hmd83/tanen/docs/TRD-001.md

  
**TanenBase Project**

Smart Hive Monitoring System

**Technical Requirements Document**

TRD-001

| Document Version | 1.0 |
| :---- | :---- |
| **Status** | DRAFT |
| **Date** | March 2026 |
| **Project** | TanenBase \- Smart Hive System |

> **Note for readers of the open-source release.** This TRD is a **DRAFT** written before implementation, kept in the repo as design intent and traceability for the acceptance criteria (AC-01 … AC-10). Where the shipped firmware deliberately differs from it \- payload width, timer implementation, join/DevNonce handling, GATT write permissions \- `ARCHITECTURE.md` and `PLAN.md` are authoritative, not this document. See "Deviations from this TRD" below.

# **1\. Document Control**

| Field | Details |
| :---- | :---- |
| **Project Name** | TanenBase — Smart Hive Monitoring System |
| **Document Type** | Technical Requirements Document (TRD) |
| **Document ID** | TRD-001 |
| **Version** | 1.0 — Initial Release |
| **Status** | DRAFT |
| **Date** | March 2026 |
| **Classification** | Confidential |

## **1.1 Revision History**

| Version | Description |
| :---- | :---- |
| **1.0** | Initial TRD drafted — all hardware, firmware, LoRa, FSM, and payload requirements defined. |

## **1.2 Definitions & Abbreviations**

| Term | Definition |
| :---- | :---- |
| **ADC** | Analog-to-Digital Converter |
| **ADR** | Adaptive Data Rate (LoRaWAN feature) |
| **BLE** | Bluetooth Low Energy |
| **FSM** | Finite State Machine |
| **LNS** | LoRa Network Server (e.g., TTN) |
| **LoRa** | Long Range radio modulation technology (Semtech SX1262) |
| **LoRaWAN** | LoRa Wide Area Network — open MAC layer protocol |
| **OTAA** | Over-the-Air Activation — LoRaWAN join procedure |
| **T\_MEAS** | Measurement Timer — interval between sensor readings |
| **T\_TX** | Transmission Timer — interval between LoRa uplinks |
| **TTN** | The Things Network — public LoRaWAN network server |
| **TRD** | Technical Requirements Document |

# **2\. Project Overview**

TanenBase is an ultra-low-power IoT end-node designed for remote, unattended beehive monitoring. Each node is deployed inside or beneath a beehive and continuously measures hive weight, internal temperature, and battery voltage. Collected data is transmitted over the LoRaWAN network to a cloud server for remote analysis and alerting.

The system is engineered for extreme power efficiency, enabling multi-year operation on a single battery charge. A Finite State Machine (FSM) governs all operational modes, ensuring that the sensor sampling schedule is fully decoupled from the radio transmission schedule. Both timers are remotely configurable via LoRaWAN downlink or locally via Bluetooth (BLE).

## **2.1 System Goals**

* Continuous, unattended monitoring of hive weight, temperature, and battery voltage.

* Ultra-low-power operation — less than 20 µA in sleep state.

* Immediate anomaly alerting for sudden weight loss (swarm detection or theft).

* Remote parameter configuration via LoRaWAN downlink and local BLE.

* Robust, binary-encoded LoRaWAN uplinks with 4-byte payload.

* Reliable OTAA network joins on the EU868 frequency plan.

# **3\. Hardware Platform**

## **3.1 Processing & Radio Module**

| Parameter | Specification |
| :---- | :---- |
| **Module** | Seeed Studio XIAO nRF54LM20A (Standard, non-Sense variant) \+ Wio-SX1262 LoRa Kit |
| **MCU** | Arm Cortex-M33 128 MHz RISC-V coprocessor 128 MHz FLPR  |
| **Flash Memory** | NVM 1.5 MB |
| **RAM** | 256 KB  RAM |
| **BLE Radio** | Integrated Bluetooth 6.0 LE (2.4 GHz) |
| **LoRa Modem** | Semtech SX1262 (mounted on Wio-SX1262 kit) |
| **Operating Voltage** | 3.3 V |

## **3.2 Sensors**

| Component | Specification & Purpose |
| :---- | :---- |
| **Load Cell ADC** | Adafruit NAU7802 24-Bit ADC — high-resolution weight measurement via I2C |
| **Temperature Sensor** | DS18B20 1-Wire digital temperature sensor — hive internal temperature |
| **Battery Monitor** | On-board Nordic nPM1300 PMIC, factory-trimmed VBAT ADC (no divider) |

## **3.3 User Interface**

| Interface Element | Hardware & Function |
| :---- | :---- |
| **LED** | System status indicator — BLE/Setup mode active \-successful LoRa transmission- LoRa join failure |
| **TanenButton** | Physical push button — triggers Setup Mode (hold 3 s) or wakes from sleep |

# **4\. Software & Operating System**

| Parameter | Specification |
| :---- | :---- |
| **Operating System** | nRF Connect SDK v3.2.4 |
| **Build System** | West (Zephyr meta-tool) |
| **LoRaWAN Stack** | Zephyr LoRaWAN subsystem (LRWAN) |
| **BLE Stack** | Zephyr Bluetooth subsystem (Nordic SoftDevice-compatible) |
| **Storage** | Zephyr Settings subsystem (NVS backend) for persistent config |
| **Power Management** | Zephyr Power Management API — lowest supported sleep state |

# **5\. LoRaWAN Requirements**

## **5.1 Network Parameters**

| Parameter | Requirement |
| :---- | :---- |
| **Radio Modem** | Semtech SX1262 — LoRa-only modem |
| **Frequency Plan** | EU868 — European 868 MHz ISM band (8 channels) |
| **Join Procedure** | OTAA (Over-the-Air Activation) — mandatory. ABP is prohibited. |
| **Device Class** | Class A — lowest power; uplink-initiated receive windows only |
| **Payload Encoding** | Binary — raw bytes only. JSON and text strings are strictly forbidden. |
| **Adaptive Data Rate** | ADR enabled — network server controls spreading factor and transmit power |
| **Confirmed Uplinks** | Unconfirmed uplinks preferred to minimize airtime; confirmed only for anomaly alerts |
| **Downlink Usage** | Used for remote configuration of T\_MEAS, T\_TX, and anomaly threshold |

## **5.2 EU868 Channel Plan**

| Channel | Frequency & Settings |
| :---- | :---- |
| **CH0** | 868.100 MHz — Spreading Factor SF7-SF12, BW 125 kHz |
| **CH1** | 868.300 MHz — Spreading Factor SF7-SF12, BW 125 kHz |
| **CH2** | 868.500 MHz — Spreading Factor SF7-SF12, BW 125 kHz |
| **CH3–CH7** | Additional channels per TTN EU868 plan (joined after OTAA) |
| **Join Channels** | CH0, CH1, CH2 used for OTAA join requests |
| **Duty Cycle** | 1% per sub-band — strictly enforced to comply with EU ETSI regulations |
| **Max EIRP** | 16 dBm (per EU868 specification) |

## **5.3 OTAA Credentials**

| Credential | Requirement |
| :---- | :---- |
| **JoinEUI (AppEUI)** | 64-bit identifier — provisioned during Setup Mode via BLE web app |
| **DevEUI** | 64-bit unique device identifier — factory-programmed or BLE-provisioned |
| **AppKey** | 128-bit AES root key — provisioned during Setup Mode via BLE web app |
| **Storage** | All credentials stored in non-volatile flash via Zephyr Settings (NVS) |

## **5.4 Downlink Command Format**

Class A RX1/RX2 after every uplink. One field per downlink (FPort selects field). User may send any subset.

| FPort | Field | Bytes | Encoding |
| :---- | :---- | :---- | :---- |
| **10** | T\_TX (`tx_interval`) | 4 | uint32 BE, seconds |
| **11** | T\_MEAS (`ms_interval`) | 4 | uint32 BE, seconds (clamped ≥ 60) |
| **12** | anomaly weight threshold | 2 | uint16 BE, grams |
| **13** | anomaly temp threshold | 2 | uint16 BE, °C × 100 |

Wrong length → ignored (warning logged). Values persisted to ZMS on receipt.

# **6\. Payload Specification**

The uplink payload is exactly 4 bytes. No padding, headers, version bytes, or metadata are permitted. The server (TTN Payload Formatter) is solely responsible for decoding raw values back to human-readable units.

## **6.1 Payload Map**

| Byte(s) | Field |
| :---- | :---- |
| **Byte 0–1 (uint16, big-endian)** | Weight — raw value \= kg × 100\. Range: 0–65535 (max 655.35 kg). Example: 45.23 kg → 4523 |
| **Byte 2 (uint8)** | Temperature — raw value \= °C rounded to nearest integer. Range: 0–255. Example: 36°C → 36 |
| **Byte 3 (uint8)** | Battery Voltage — raw value \= V × 10\. Range: 0–255 (max 25.5 V). Example: 12.4 V → 124 |

## **6.2 Payload Encoding Rules**

* Total payload length: exactly 4 bytes. Never more, never less.

* Weight field: multiply float kg value by 100, cast to uint16, pack as big-endian.

* Temperature field: round float °C value to nearest integer, cast to uint8.

* Voltage field: multiply float V value by 10, cast to uint8.

* Fields must be packed in the order: Weight (2B), Temperature (1B), Voltage (1B).

* No null bytes, no struct padding, no alignment bytes between fields.

* JSON, CSV, or ASCII text payloads are prohibited and constitute a firmware defect.

## **6.3 TTN Payload Decoder (Reference JavaScript)**

function decodeUplink(input) {

  var b \= input.bytes;  
  return { decoded\_payload: {  
    weight\_kg:  ((b\[0\] \<\< 8\) | b\[1\]) / 100.0,  
    temperature\_c: b\[2\],  
    voltage\_v:   b\[3\] / 10.0  
  }};

}

# **7\. Cycle Control & Power Management**

The sensor measurement schedule and the LoRaWAN transmission schedule are fully independent. Two configurable timers govern system wake cycles.

## **7.1 Timer Parameters**

| Parameter | Specification |
| :---- | :---- |
| **T\_MEAS** | Measurement Timer — minimum 1 minute. Configurable remotely via LoRaWAN downlink or BLE. |
| **T\_TX** | Transmission Timer — must satisfy: T\_TX ≥ T\_MEAS at all times. |
| **Remote Config** | Both timers are remotely adjustable via LoRaWAN downlink command or BLE Setup Mode. |
| **Constraint Enforcement** | Firmware must reject any downlink that sets T\_TX \< T\_MEAS and respond with a NACK. |
| **Default T\_MEAS** | 15 minutes (900 seconds) |
| **Default T\_TX** | 60 minutes (3600 seconds) |

## **7.2 Measurement Routine**

* Wake processor from deep sleep.

* Power up load cell (NAU7802) and DS18B20 .

* Acquire N consecutive weight samples (default N \= 10\) at regular intervals.

* Compute arithmetic mean weight; discard outliers exceeding ±2σ to suppress wind noise.

* Acquire single temperature reading from DS18B20.

* Acquire single battery voltage reading via internal ADC.

* Compare new mean weight to last stored weight; check for anomaly threshold breach.

* Store all readings in SRAM (latest snapshot only — no historical buffer required).

* Power down all sensors immediately after data acquisition.

* Transition to FSM State 4 (Active Sleep) or State 3 (Transmission) based on anomaly flag.

## **7.3 Transmission Routine**

* Wake processor from deep sleep.

* Load latest sensor snapshot from SRAM.

* Encode 4-byte binary payload per Section 6 specification.

* Power up SX1262 LoRa radio via SPI.

* Transmit uplink on next available channel (duty cycle compliant).

* Hold radio active for RX1 window (1 second delay) and RX2 window (2 seconds delay) to receive downlink.

* Process any received downlink configuration commands.

* Power down SX1262 radio (all GPIO lines low, SPI bus released).

* Return to FSM State 4 (Active Sleep).

## **7.4 Emergency Anomaly Override**

| Parameter | Specification |
| :---- | :---- |
| **Trigger Condition** | New mean weight \< (last stored weight − anomaly threshold) |
| **Default Threshold** | 2.0 kg (200 raw units). Configurable via downlink or BLE. |
| **Action** | Abort T\_TX wait. Immediately enter State 3 (Transmission).  LED blink |
| **Uplink Type** | Confirmed uplink used for anomaly alerts to guarantee delivery. |
| **Alert Payload** | Standard 4-byte payload — server infers anomaly from weight delta via TTN decoder. |

# **8\. Finite State Machine (FSM)**

The firmware implements a strict four-state FSM. No state may be entered except through its defined entry conditions. All transitions are deterministic.

| State 1: Setup Mode (BLE) |  |
| :---- | :---- |
| **Entry** | Initial device boot OR TanenButton held for ≥3 seconds. |
| **LED State** | solid ON throughout Setup Mode. |
| **BLE** | Activate Bluetooth LE. Advertise as 'TanenBase-XXXX' (last 4 hex of DevEUI). |
| **Web App** | Serve configuration interface via connected BLE client (HTML \+ JS web app one file index.html). |
| **Config Items** | LoRaWAN credentials (JoinEUI, DevEUI, AppKey), T\_MEAS, T\_TX, anomaly threshold, scale calibration (zero offset, scale factor) \-read(expt AppKey  )-write(save). |
| **Live Feed** | Broadcast real-time sensor data over BLE NOTIFY characteristic for scale tare/calibration. |
| **Test Join** | Execute LoRaWAN OTAA test join on user request from web app. Report result (Blink 1Hz \= OK, fast= fail). |
| **Exit — Normal** | Exit button in web app . BLE advertisement stopped. Transition to State 4\. |
| **Exit — Timeout** | 5-minute inactivity timeout reached without user interaction. BLE stopped. Transition to State 4\. |

| State 2: Measurement State |  |
| :---- | :---- |
| **Entry** | T\_MEAS timer expiration in State 4\. |
| **LED State** | No LED activity during measurement (power conservation). |
| **Sensor Power** | Wake up NAU7802 and DS18B20 .NAU7802 requires time 600ms  to stabilize |
| **Weight Acquisition** | Capture N \= 10 samples from NAU7802 ADC. Compute filtered mean weight (kg). |
| **Temp Acquisition** | Issue single read command to DS18B20. Store integer °C value. |
| **Voltage Acquisition** | VBAT Enable pin then Sample internal ADC on voltage-divider channe(P1.13 AIN6\_VBAT)l. Store (V × 10\) uint8 value. |
| **Anomaly Check** | If (new weight) \< (last weight − threshold): set ANOMALY flag. |
| **Data Save** | Update SRAM sensor snapshot with new values. |
| **Exit — Anomaly** | ANOMALY flag set → transition immediately to State 3 (Transmission). |
| **Exit — Normal** | No anomaly → transition to State 4 (Active Sleep). |

| State 3: Transmission State |  |
| :---- | :---- |
| **Entry** | T\_TX timer expiration in State 4 OR ANOMALY flag set in State 2\. |
| **LED State** | LED — blinks once per transmit attempt. blinks fat — lit on join failure or anomaly uplink. |
| **Payload Build** | Encode 4-byte binary payload: bytes \[0:1\] \= weight × 100 (uint16 BE), byte \[2\] \= temp (uint8), byte \[3\] \= voltage × 10 (uint8). |
| **Radio Power** | Assert SPI CS and power enable for SX1262. |
| **Transmit** | Send uplink frame (unconfirmed normally; confirmed if ANOMALY flag set). |
| **RX Windows** | Wait for RX1 ( 5 s window) and RX2 (6 s window). Process any downlink. |
| **Downlink Handling** | Apply new T\_MEAS, T\_TX, or anomaly threshold from downlink. Validate T\_TX ≥ T\_MEAS. |
| **Radio Power Down** | De-assert all SX1262 control lines. Release SPI bus. |
| **Clear Flag** | Clear ANOMALY flag. |
| **Exit** | Always transition to State 4 (Active Sleep). |

| State 4: Active Sleep State |  |
| :---- | :---- |
| **Entry** | Completion of State 1, State 2, or State 3\. |
| **LED State** | All LEDs OFF. |
| **Sensor Power** | NAU7802 powered down (AVDDS=1, PUA=0 \-\> \~0.1 uA)-powered down DS18B20 I2C pins during low-power modes, they should generally be configured as inputs (high-impedance) or as outputs driven high to avoid leaking current through external pull-up resistors |
| **Radio Power** | SX1262 in SLEEP mode. SPI bus idle. BLE radio disabled. |
| **MCU Sleep** | nRF54LM20A enters System OFF \+ GRTC \+ RAM retention (stack \+ essentials) |
| **Power Budget** | Total system current draw: ≤ 20 µA. |
| **Timer Operation** | Both T\_MEAS and T\_TX GRTC  timers continue running during sleep . |
| **Exit — T\_MEAS** | T\_MEAS expires first → wake to State 2 (Measurement). |
| **Exit — T\_TX** | T\_TX expires first → wake to State 3 (Transmission). |
| **Exit — Button** | TanenButton pressed → wake to State 1 (Setup Mode). |

# **9\. FSM State Transition Summary**

| From State | Event | To State | Condition |
| :---- | :---- | :---- | :---- |
| State 4 (Sleep) | T\_MEAS expires | State 2 (Measurement) | Normal measurement cycle |
| State 4 (Sleep) | T\_TX expires | State 3 (Transmission) | Normal transmission cycle |
| State 4 (Sleep) | TanenButton pressed | State 1 (Setup) | User-initiated configuration |
| State 2 (Measurement) | No anomaly detected | State 4 (Sleep) | Normal exit |
| State 2 (Measurement) | Anomaly flag set | State 3 (Transmission) | Emergency override |
| State 3 (Transmission) | Transmission complete | State 4 (Sleep) | Always |
| State 1 (Setup) | Config saved | State 4 (Sleep) | Normal exit |
| State 1 (Setup) | 5-min inactivity | State 4 (Sleep) | Timeout exit |
| Any State | TanenButton (3 s hold) | State 1 (Setup) | From sleep only; immediate boot entry always |

# **10\. Power Budget**

| System Mode | Target Current Draw |
| :---- | :---- |
| **State 4 — Active Sleep (MCU deep sleep, all peripherals off)** | ≤ 20 µA (absolute maximum) |
| **State 2 — Measurement (sensors powered, ADC active)** | \< 15 mA peak |
| **State 3 — LoRa TX (SX1262 transmitting at \+14 dBm)** | ≈ 120 mA peak (limited duration) |
| **State 3 — LoRa RX window** | ≈ 5 mA |
| **State 1 — BLE advertising** | ≈ 3–5 mA |
| **Target Battery Life** | \> 12 months on a primary cell (typical deployment). As built: **~4.6 years** on 3× AAA Li/FeS₂ at 15 min / 2 h (~3.3 years with Extended Mode BLE sensors, 139 mC per TX wake) — see the deviations table and `docs/POWER_BUDGET.md` §5. |

## **10.1 Power Management Rules**

* SX1262 must be commanded to SLEEP mode before the nRF54LM20A enters deep sleep.

* BLE radio must be fully disabled before entering State 4\.

* No floating GPIO pins that could increase leakage current above the 20 µA target.

# **11\. Configuration Parameters**

All configuration parameters must be stored in non-volatile memory (NVS flash) using the Zephyr Settings subsystem. Parameters survive power cycles and hardware resets.

| Parameter | Type |
| :---- | :---- |
| **JoinEUI (AppEUI)** | uint8\[8\] — 64-bit LoRaWAN join identifier |
| **DevEUI** | uint8\[8\] — 64-bit device unique identifier |
| **AppKey** | uint8\[16\] — 128-bit AES root key |
| **T\_MEAS** | uint32 — measurement interval in seconds (min: 60 s) |
| **T\_TX** | uint32 — transmission interval in seconds (constraint: T\_TX ≥ T\_MEAS) |
| **Anomaly Threshold** | uint16 — weight drop trigger in grams (default: 2000 g) |
| **Scale Zero Offset** | int32 — NAU7802 raw ADC offset at zero load |
| **Scale Factor** | float32 — NAU7802 calibration factor (raw ADC counts per kg) |
| **N\_SAMPLES** | uint8 — number of weight samples per measurement cycle (default: 10\) |

# **12\. BLE Configuration Interface**

## **12.1 BLE Profile**

| Parameter | Specification |
| :---- | :---- |
| **Advertisement Name** | 'TanenBase-XXXX' where XXXX \= last 4 hex digits of DevEUI |
| **Transport** | BLE GATT — custom service with characteristics for each config group |
| **Security** | Encrypted BLE pairing required before credential write is permitted |
| **Web App** | Browser-based HTML \+ JavaScript configuration interface (no app install required one file index.html) save configurations success or failed  as notify in web app  |
| **Live Calibration** | NOTIFY characteristic streams real-time weight, temperature, voltage at 1 Hz during State 1 (Setup) |
| **Test lorawan connection** | User can **Test lorawan connection**  via BLE command. Result reported via LED and BLE notification. |

## **12.2 BLE GATT Service Structure**

| Characteristic | Properties & Description |
| :---- | :---- |
| **Device Info** | READ — DevEUI, firmware version, current timer settings |
| **LoRaWAN Credentials** | JoinEUI, AppKey \-DevEUI |
| **Timer Config** | READ \+ WRITE — T\_MEAS, T\_TX values in seconds |
| **Anomaly Config** | READ \+ WRITE — anomaly threshold in grams |
| **Scale Calibration** | READ \+ WRITE — zero offset, scale factor; WRITE TARE command |
| **Live Sensor Feed** | NOTIFY — real-time weight (g), temperature (°C), voltage (V) at 1 Hz |
| **Network Test** | WRITE — command byte 0x01 triggers Lora test test; READ returns last result |

# **13\. Non-Functional Requirements**

## **13.1 Reliability**

* LoRaWAN OTAA join must be retried up to 8 times with exponential backoff on failure.

* If OTAA join fails after all retries, the device must enter State 4 and retry at next T\_TX interval.

* Watchdog timer must be active at all times. WDT timeout: 60 seconds.

* All NVS write operations must be atomic — partial writes must not corrupt configuration.

## **13.2 Environmental**

* Operating temperature: \-20°C to \+60°C (outdoor beehive deployment).

* Humidity: 95% RH non-condensing.

* All connectors must be weatherproofed. Enclosure minimum IP65.

## **13.3 Security**

* AppKey must never be logged to serial/debug output.

## **13.4 Regulatory**

* EU868 duty cycle limits (1% per sub-band) must be enforced in firmware via LoRaWAN stack.

* RF output power must not exceed \+16 dBm EIRP (EU868 limit).

* Device must comply with CE marking requirements for short-range radio devices (EN 300 220).

# **14\. Acceptance Criteria**

| ID | Acceptance Test |
| :---- | :---- |
| **AC-01** | Device joins TTN via OTAA on EU868 within 3 attempts from cold start. |
| **AC-02** | 4-byte uplink payload received at TTN; decoded weight, temperature, voltage match measured values within tolerance. |
| **AC-03** | Sleep current measured ≤ 20 µA with all peripherals powered down. |
| **AC-04** | Anomaly alert uplink transmitted within 5 seconds of weight drop exceeding threshold. |
| **AC-05** | TanenButton held 3 s triggers Setup Mode ( LED ON, BLE advertising starts). |
| **AC-06** | 5-minute BLE inactivity timeout exits Setup Mode and resumes normal operation. |
| **AC-07** | T\_TX downlink command updates timer; T\_TX \< T\_MEAS downlink is rejected. |
| **AC-08** | Weight readings averaged over N \= 10 samples; single-sample noise suppressed. |
| **AC-09** | All configuration parameters persist after power cycle (NVS integrity test). |
| **AC-10** | Firmware watchdog resets device if main loop stalls for ≥60 seconds. |

Pins Map 

XIAO header *roles* are identical to the original nRF54L15 build \- only the
underlying GPIO numbers differ, so the same carrier PCB fits both modules.

| XIAO Pin | nRF54LM20A GPIO | Function/Notes |
| :---: | :---: | :---: |
| D0 | P1.00 | DS18B20 data (1-Wire). Wio-SX1262 ships K1 button \+ 10K pull-up on this net \- the trace MUST be cut; with it fitted 1-Wire does not read at all |
| D1 | P1.31 | DIO1 |
| D2 | P1.30 | RST (Reset) \+ External Tanen Key (bare switch to GND) \- System OFF wake source |
| D3 | P1.29 | BUSY |
| D4 | P1.03 | NSS (SPI chip select), spi23 |
| D5 | P1.07 | LORA\_RF\_SW1 \- Wio-SX1262 antenna switch control. Not a spare GPIO \- do not repurpose as input/button |
| D6/TX | P1.08 | Software-I2C SCL for NAU7802 (uart21 and i2c22 disabled in overlay) |
| D7/RX | P1.09 | Software-I2C SDA for NAU7802 |
| D8/SCK | P1.04 | SCK (SPI clock), spi23 |
| D9/MISO | P1.05 | MISO, spi23 |
| D10/MOSI | P1.06 | MOSI, spi23 |

\-----Additional System GPIOs

| Function | Pin | Notes |
| ----- | ----- | ----- |
| **User LED** | P1.22 / P1.23 / P1.24 | On-board RGB LEDs, **active HIGH** |
| **User Key** | P0.09 | Tanen Key \- on-board button, System OFF wake source |
| **External Key** | P1.30 (D2) | Second Tanen Key, sharing the SX1262 NRESET net. Identical behaviour \- either button wakes into SETUP; `power.c` OR-s the two GPIO latches. Asleep the pin is input \+ pull-up \+ SENSE\_LOW, so the pull-up holds NRESET high; a press wakes the SoC and resets the radio, which is free because every wake is a full reset anyway. Awake the pin is an sx126x driver output, so a press is not latched \- ~0.2 % of the time, given 185 s awake/day. Moved from P0.00 (D19) on 2026-09-07: D2 is on a 7-pin header the carrier already routes, D19 was a bottom pad needing a flying wire. Any wake-capable port works (P0/P1/P3); P2 cannot wake at all. **Field-verified 2026-09-09.** |
| **PMIC I2C** | SCL P1.17 / SDA P1.18 | Bit-banged I2C to the on-board nPM1300. The board DTS wrongly declares P1.15/P1.16; corrected in the app overlay. |
| **Battery Voltage** | via nPM1300 | Factory-trimmed VBAT ADC read over `pmic_i2c`. No divider, no enable GPIO, no calibration factor. |
| **On-board NOR flash** | P2.00 \- P2.05 | py25q64 on spi00. **Never drive these from software** \- see `power.c`. Must be put into deep power-down before System OFF. |

**Document Approval**

| Role | Name / Signature / Date |
| :---- | :---- |
| **Prepared by** | Hussein Daj |
| **Reviewed by** |  |
| **Approved by** |  |

---

# **Deviations from this TRD (as-built)**

The firmware in this repository intentionally departs from the draft above.
These are design decisions, not defects.

| Area | TRD says | As built | Why |
| ----- | ----- | ----- | ----- |
| **Uplink payload** | 4 bytes | **8 bytes**: weight u24 g (0-999000), temp i16 centi-degC, battery u16 mV, flags u8 | u16 grams topped out at 65.535 kg, well under a loaded hive. Sentinels `0xFFFFFF` / `0xFFFF` / `0x7FFF` mark a failed sensor and decode to `null`. |
| **T\_TX timer** | Second hardware timer | Heartbeat **modulo** of measurement cycles (`meas_count % (tx_interval/ms_interval)`) | One GRTC wake source instead of two; no second timer to keep alive through System OFF. |
| **Uplink policy** | Fixed confirmed-uplink rules | Delta-based TX with an anomaly ladder (`src/drivers/lora.c`) | Sends on change, not on schedule \- large airtime and energy saving. |
| **DevNonce** | Not specified | Monotonic counter persisted in ZMS (ID 1), hard-fail if it cannot be written | A repeated nonce is replay-rejected by TTN, which bricks joins until the device is re-registered. |
| **Credential GATT writes** | Encrypted pairing required (12.1) | Plain read/write | Web Bluetooth has no `pair()` API; an OS-triggered SMP pairing mid-write hung the link to supervision timeout. Confidentiality now rests on BLE proximity. Tried and reverted 2026-07-07 \- see `OPEN_QUESTIONS.md` item 10. |
| **Watchdog** | 120 s, production only | `task_wdt` 60 s channel \+ `wdt31` hardware fallback, **all** builds | Meets AC-10 with margin and catches kernel/timer death, not just main-loop stalls. |
| **Battery monitor** | Voltage divider \+ SoC ADC | nPM1300 VBAT ADC | The LM20A module carries the PMIC; its ADC is factory-trimmed, so the divider and its calibration factor are gone. |
| **Battery pack** | 3.6 V / 19 Ah Li-SOCl2 single cell (10.0) | **3× AAA 1.5 V Li/FeS₂ in series** — 1200 mAh, 4.5 V nominal, 5.2 V measured fresh | Buildable, no passivation, −40 °C rated, 10× pulse margin. Costs life (4.6 y at 15 min / 2 h) and runs **above the nPM1300's 4.45 V recommended VBAT maximum for essentially its whole life** (µA-drain Li/FeS₂ plateau ~1.79 V/cell, rising with temperature); worst-case fresh pack 5.49 V against the 5.5 V absolute maximum. Accepted deviation, `docs/POWER_BUDGET.md` §5.2. |
| **Storage** | NVS, 4 KB | **ZMS**, 36 KB at 0x1D1000 (pinned in `pm_static.yml`) | `settings_zms` is unreliable on nRF54L RRAM, so `config.c` drives ZMS directly. The address is pinned so an app-size change or MCUboot adoption cannot relocate it and wipe the DevNonce. |
