hmd83/tanen/docs/LoRa uplink.png

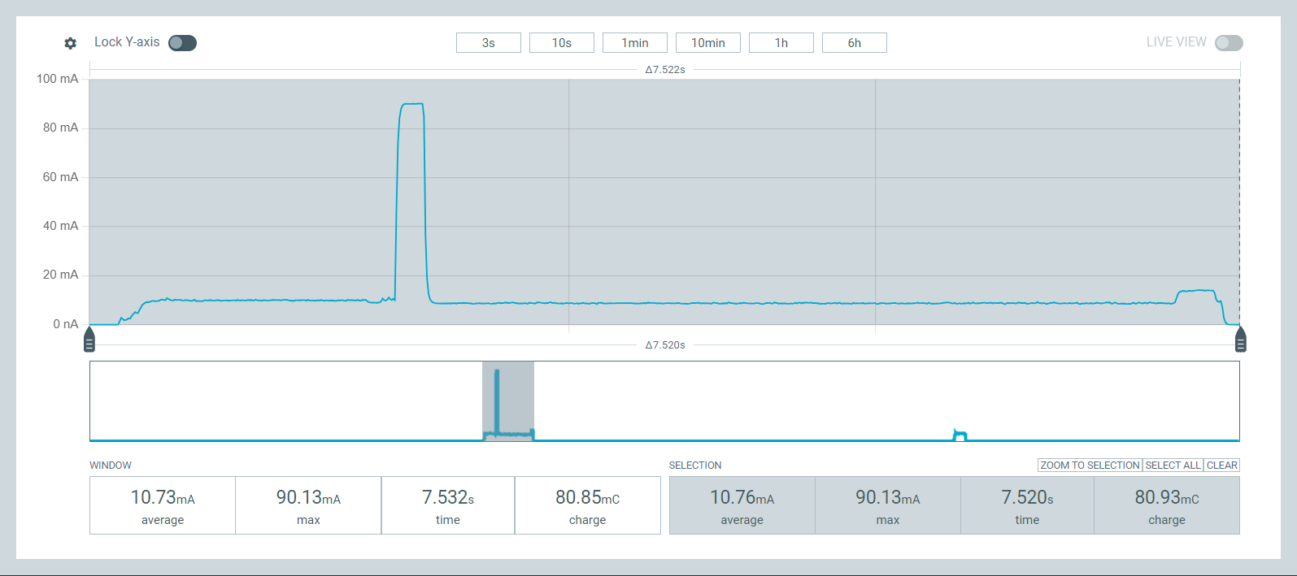
docs/LoRa uplink.png
