hmd83/tanen/site/media/ble-sensor-label.jpg

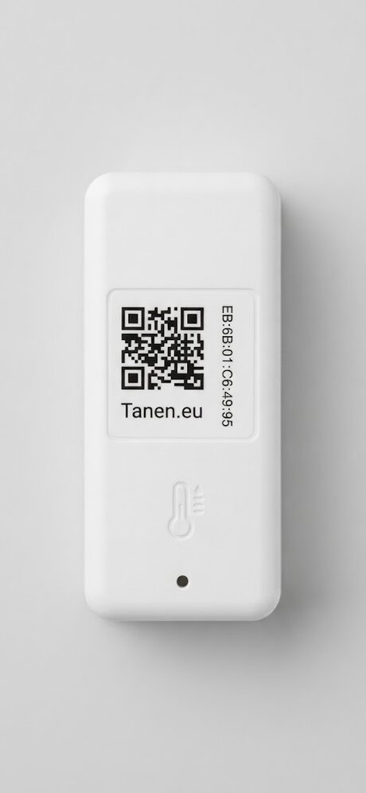
site/media/ble-sensor-label.jpg
