hmd83/tanen/Tanen_Base_pcb/simulation_image_bottom.png

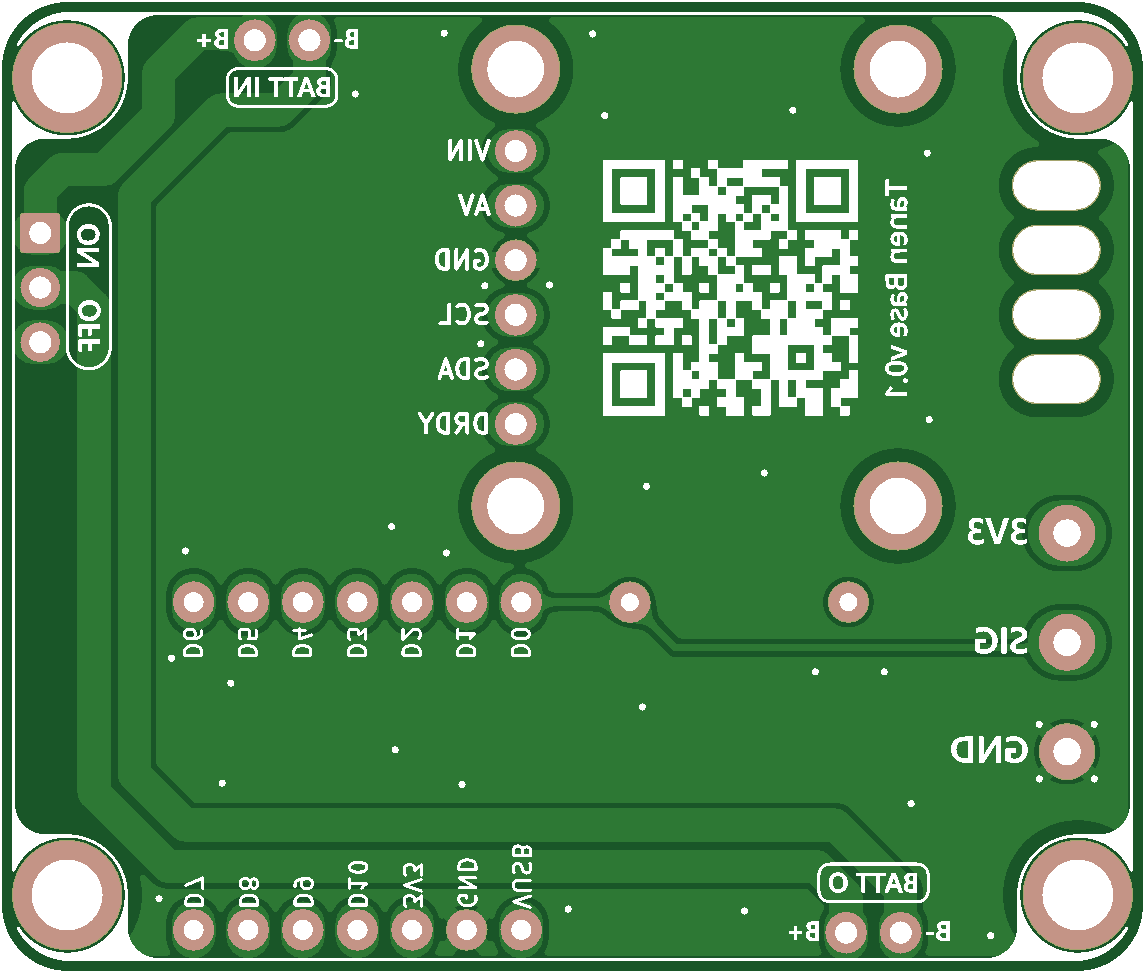
Tanen_Base_pcb/simulation_image_bottom.png
