hmd83/tanen/Tanen_Base_pcb/simulation_image_top.png

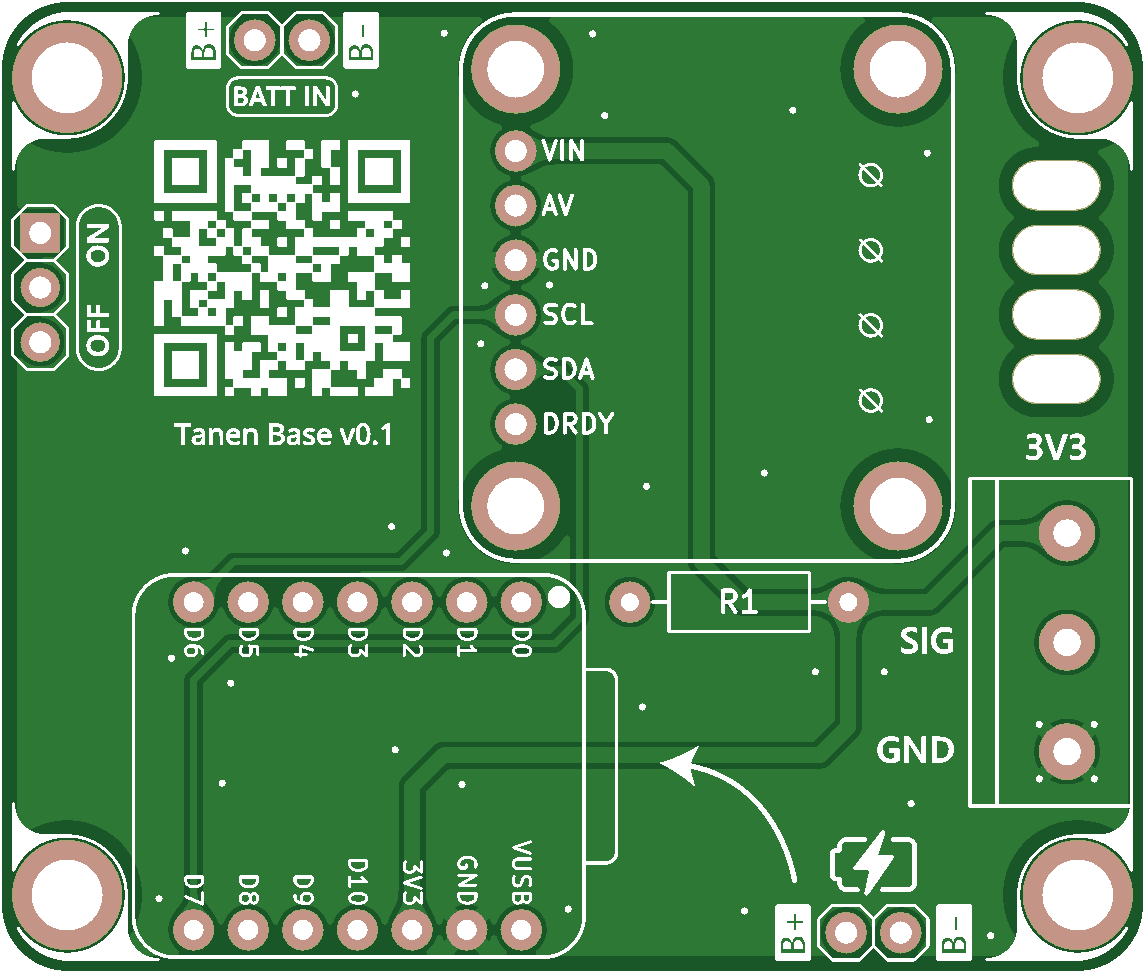
Tanen_Base_pcb/simulation_image_top.png
